Sphinkie/VintageRadio/3D models/model-view-2026-06-01.png

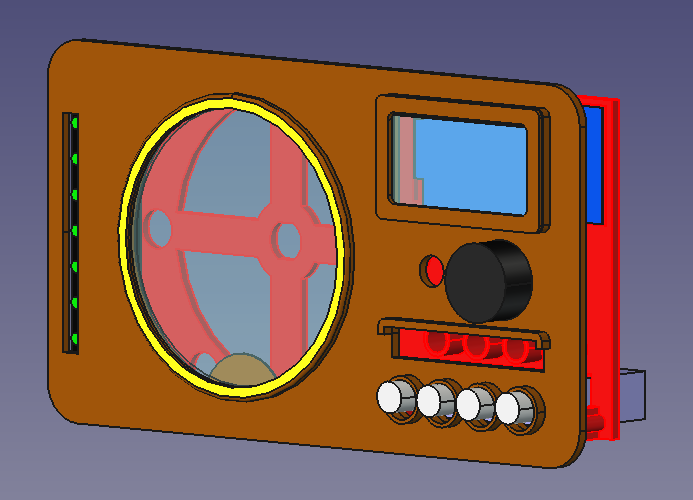
3D models/model-view-2026-06-01.png
