Sphinkie/VintageRadio/electronics/Components/datasheets/ePaper-Driver-HAT-features.png

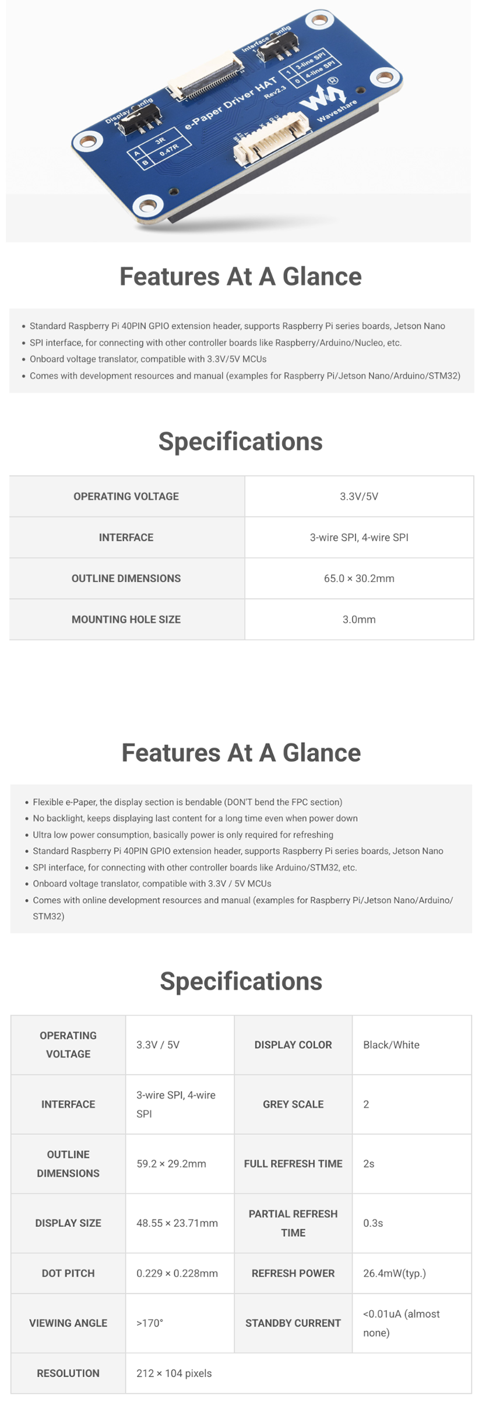
electronics/Components/datasheets/ePaper-Driver-HAT-features.png
