Sphinkie/VintageRadio/electronics/Components/datasheets/ePaper-Driver-HAT-size.png

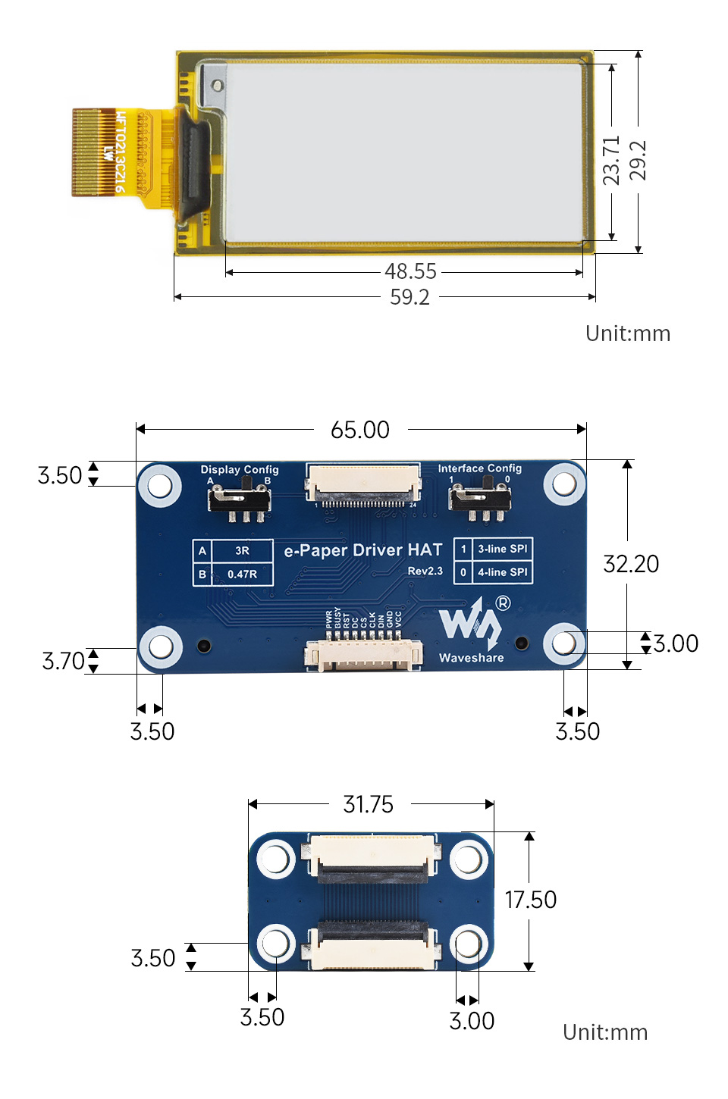
electronics/Components/datasheets/ePaper-Driver-HAT-size.png
