Sphinkie/VintageRadio/electronics/Components/datasheets/ePaper-Driver-HAT.png

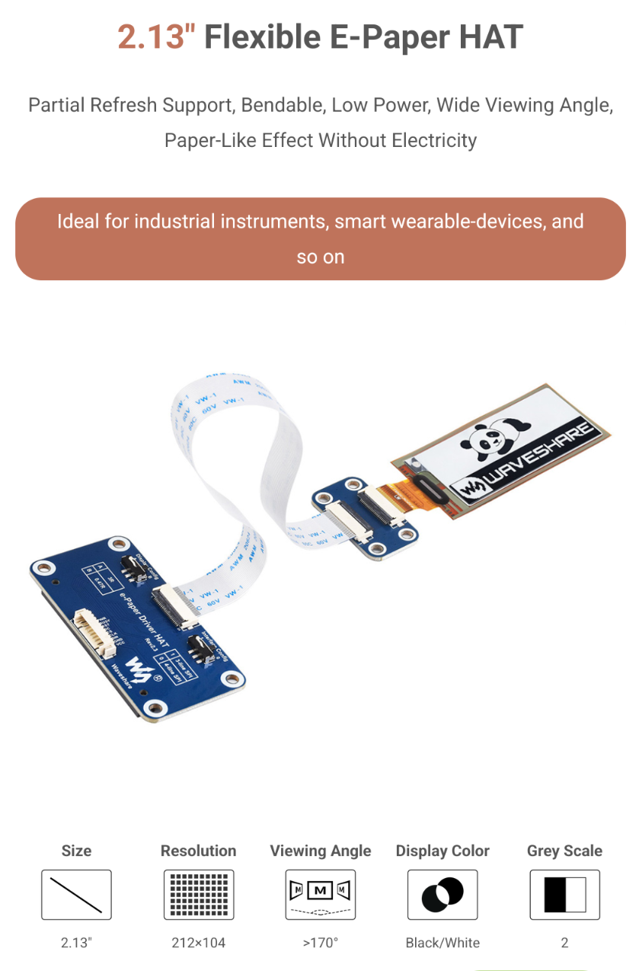
electronics/Components/datasheets/ePaper-Driver-HAT.png
