Sphinkie/VintageRadio/electronics/Components/datasheets/ePaper-Features.png

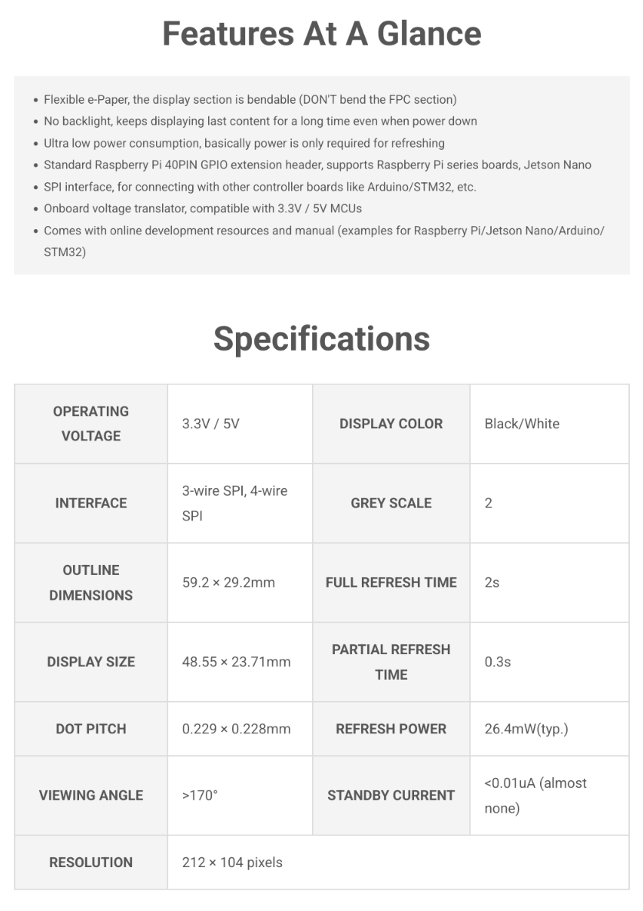
electronics/Components/datasheets/ePaper-Features.png
