Sphinkie/VintageRadio/electronics/Components/datasheets/RPI-3B-GPIO-Pinout.png

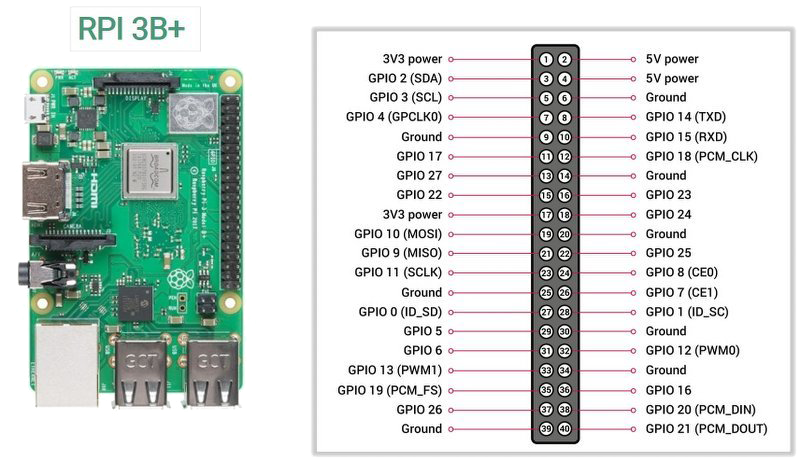
electronics/Components/datasheets/RPI-3B-GPIO-Pinout.png
