Sphinkie/VintageRadio/electronics/Components/datasheets/SN74HCS595_Pinout.png

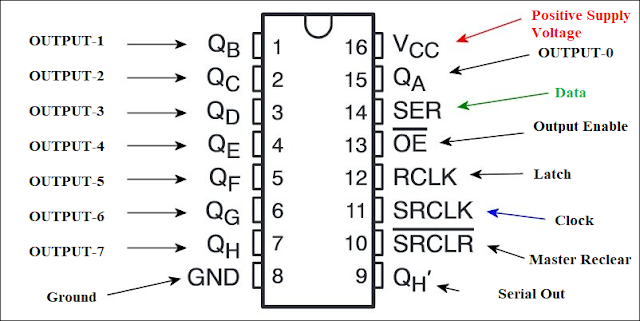
electronics/Components/datasheets/SN74HCS595_Pinout.png
