Sphinkie/VintageRadio/electronics/Components/images/ePaper-Driver-HAT-details.png

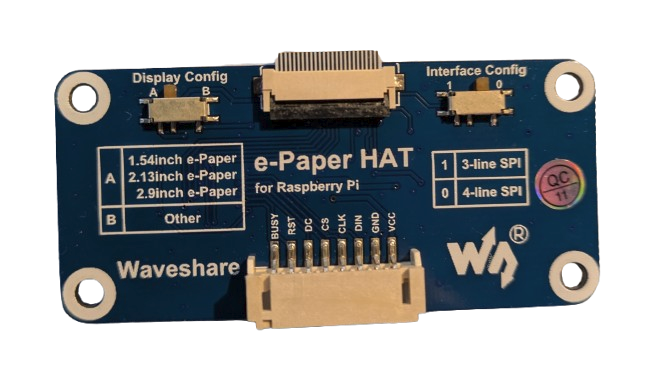
electronics/Components/images/ePaper-Driver-HAT-details.png
