Sphinkie/VintageRadio/electronics/Components/images/ePaper-Driver-HAT-wired.png

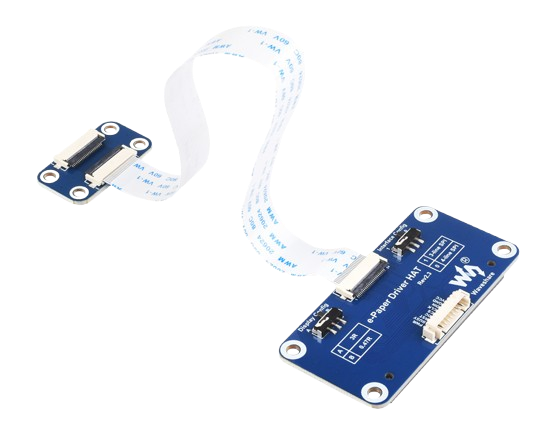
electronics/Components/images/ePaper-Driver-HAT-wired.png
