Sphinkie/VintageRadio/electronics/Components/images/ePaper-Flexible.png

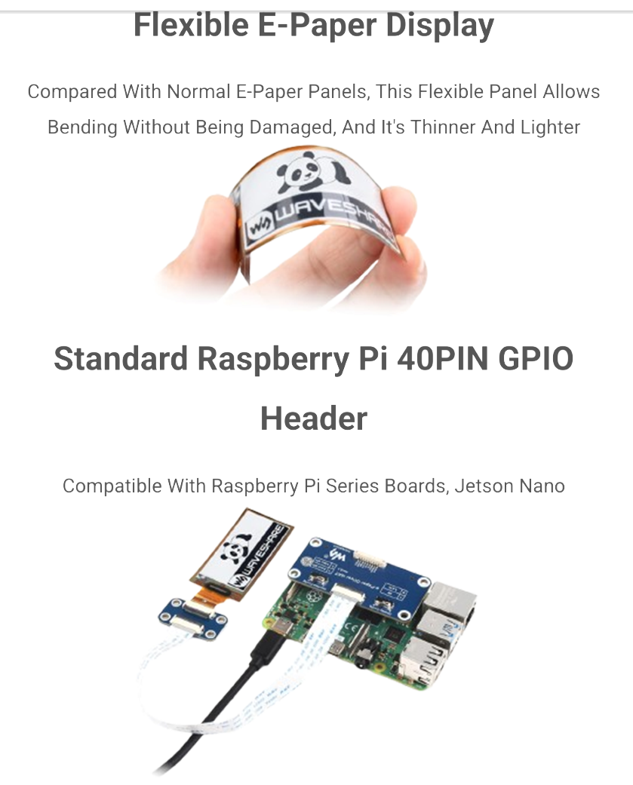
electronics/Components/images/ePaper-Flexible.png
