Sphinkie/VintageRadio/electronics/Extension boards/Extension_board.drawio.png

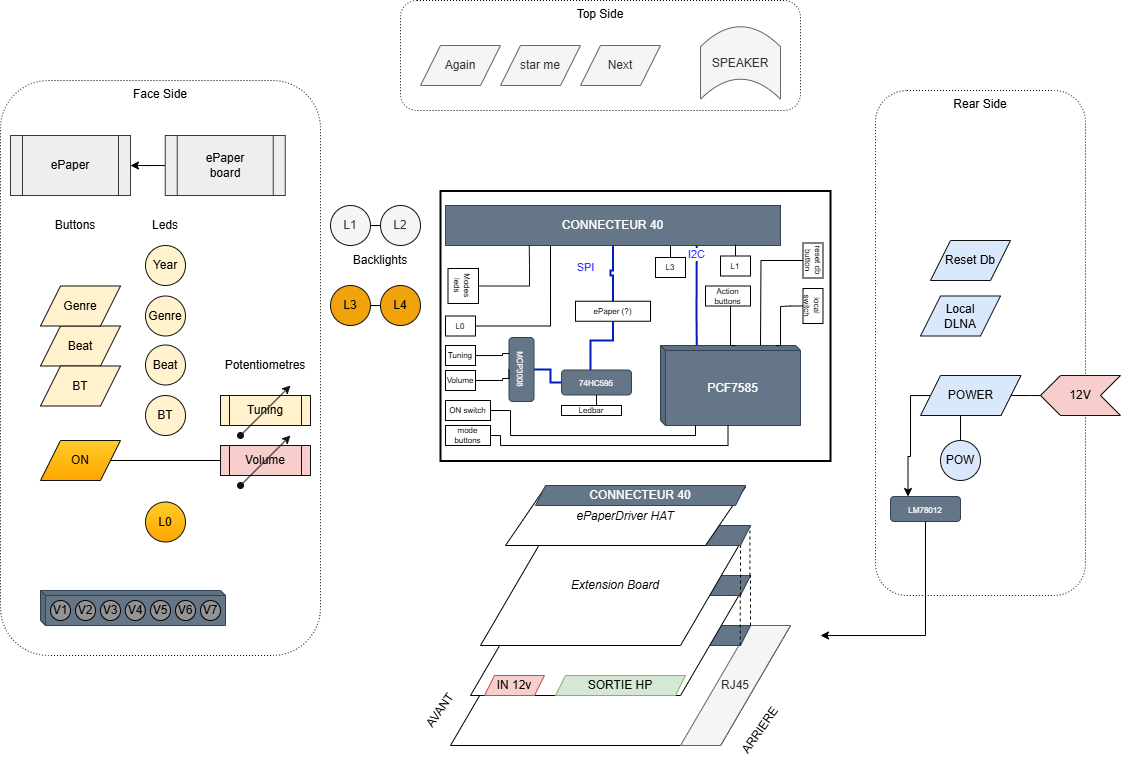
electronics/Extension boards/Extension_board.drawio.png
