Sphinkie/VintageRadio/mechanical/3mf/VintageRadio-Face_Avant.png

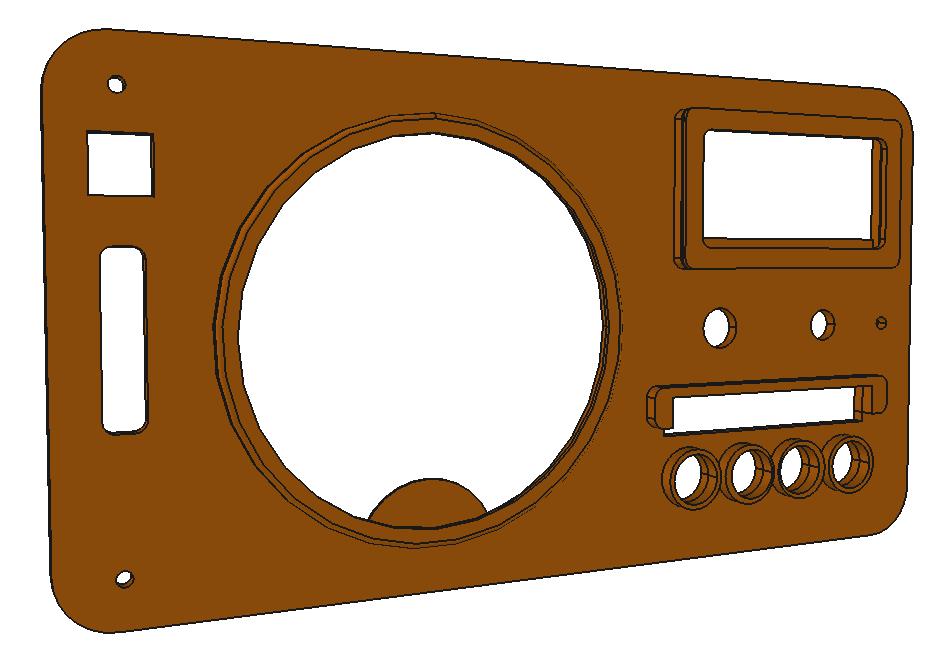
mechanical/3mf/VintageRadio-Face_Avant.png
