Sphinkie/VintageRadio/mechanical/3mf/VintageRadio-Plexi.png

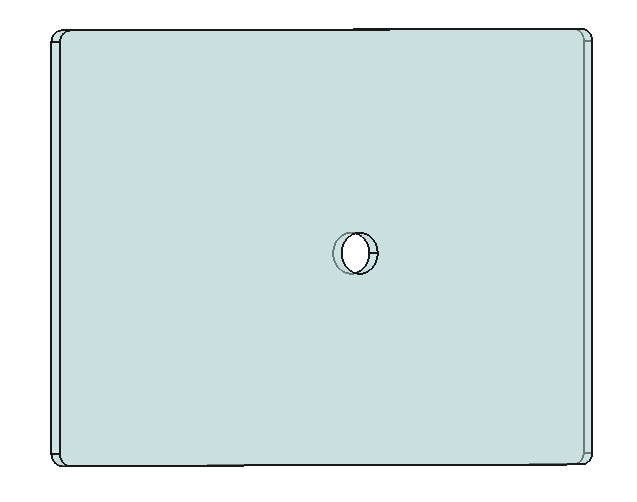
mechanical/3mf/VintageRadio-Plexi.png
