Sphinkie/VintageRadio/mechanical/3mf/VintageRadio-Support_ePaper-1.png

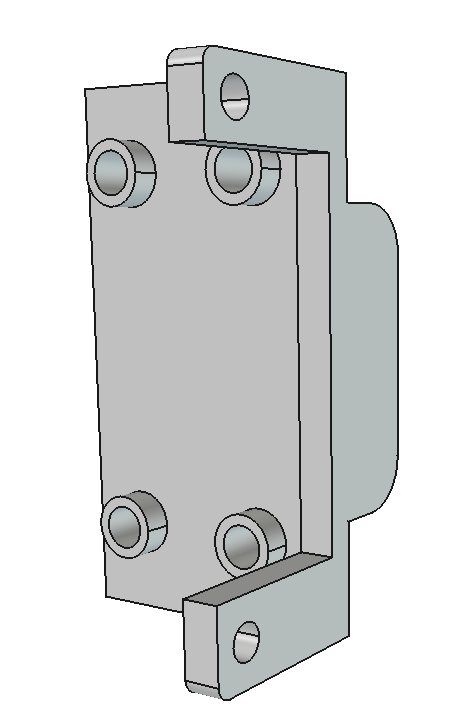
mechanical/3mf/VintageRadio-Support_ePaper-1.png
