Sphinkie/VintageRadio/mechanical/3mf/VintageRadio-Support_ePaper-3.png

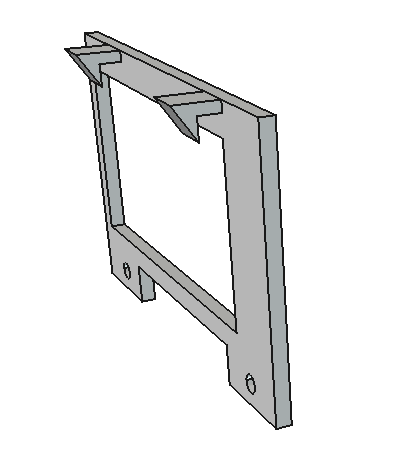
mechanical/3mf/VintageRadio-Support_ePaper-3.png
