Sphinkie/VintageRadio/mechanical/3mf/VintageRadio-Support_Leds_E10.png

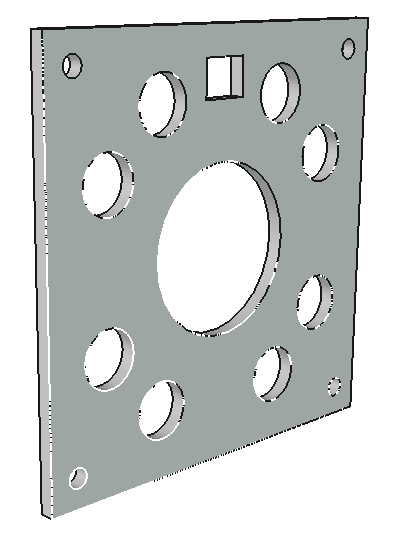
mechanical/3mf/VintageRadio-Support_Leds_E10.png
