Sphinkie/VintageRadio/mechanical/model-view-2026-04-13.png

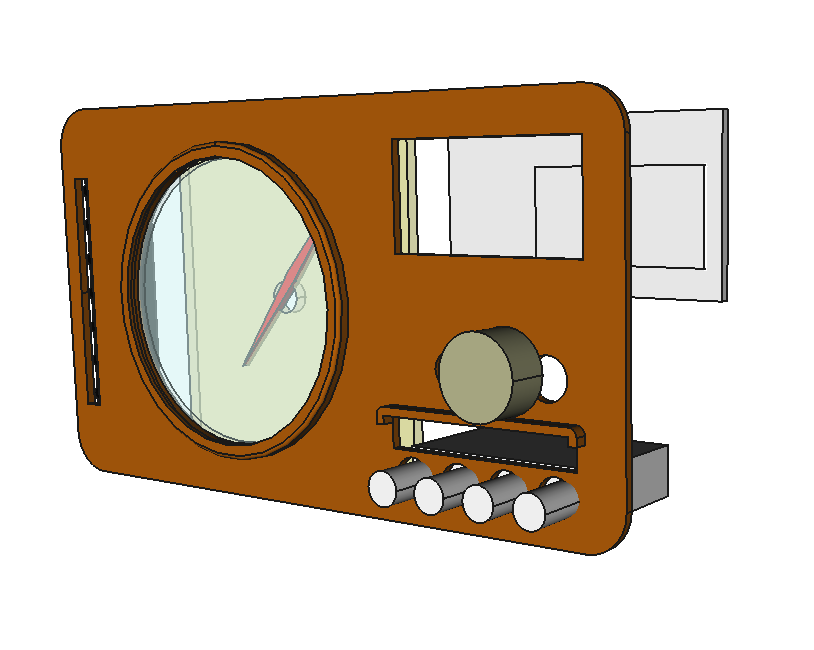
mechanical/model-view-2026-04-13.png
