Sphinkie/VintageRadio/mechanical/model-view-2026-05-31.png

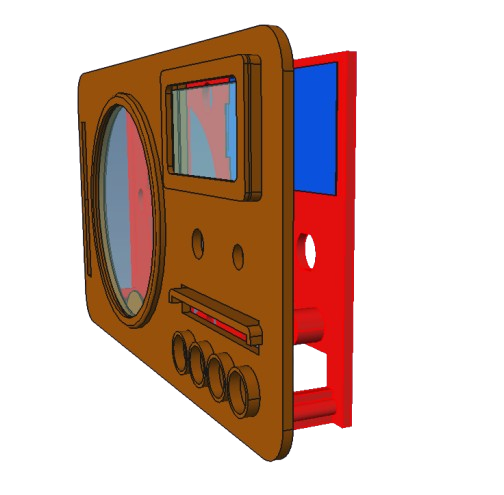
mechanical/model-view-2026-05-31.png
