Sphinkie/VintageRadio/medias/maquette.png

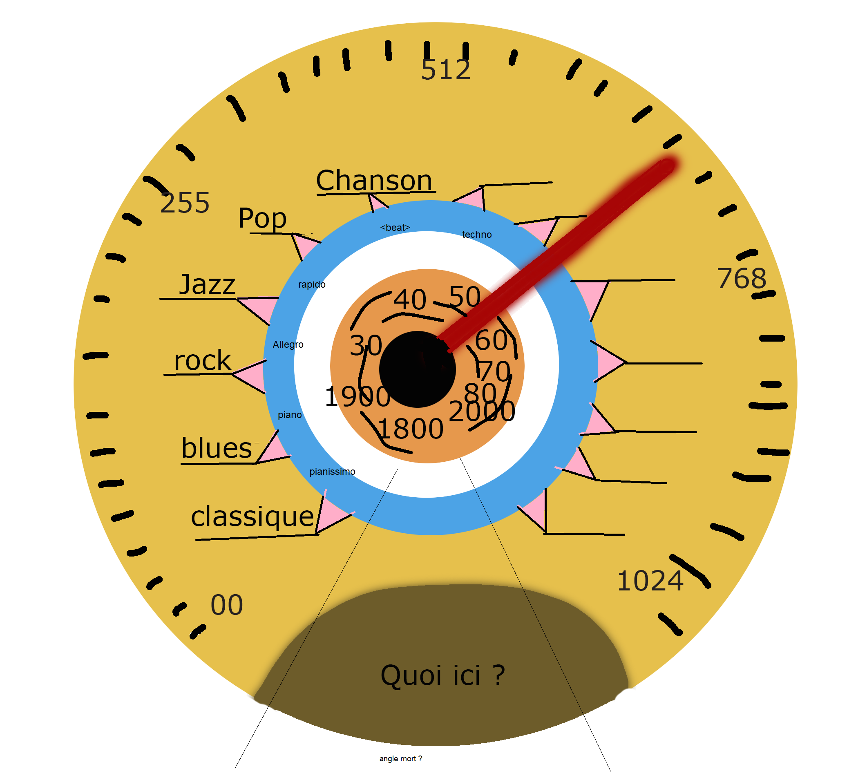
medias/maquette.png
