Sphinkie/VintageRadio/medias/pour inspiration/zoom-03.png

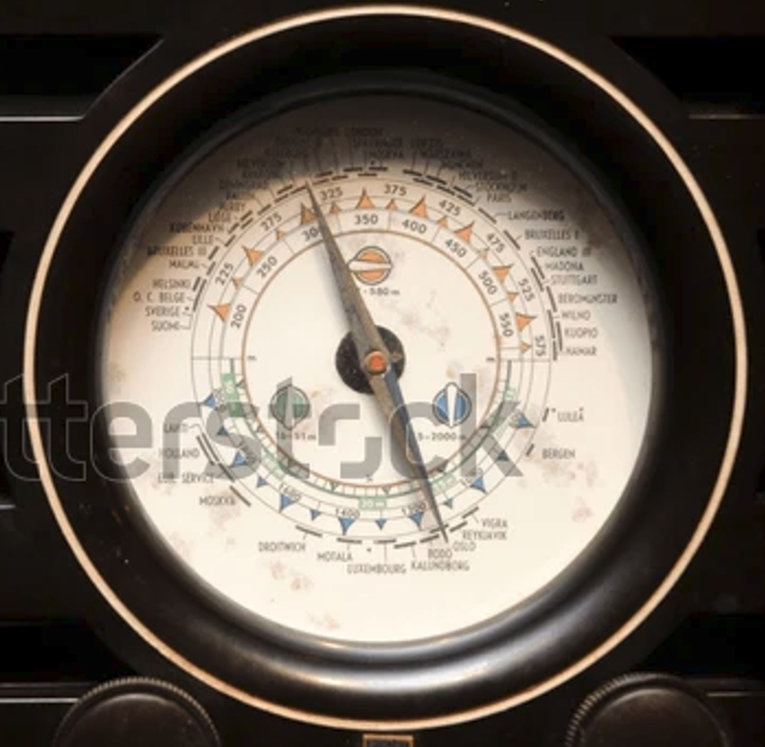
medias/pour inspiration/zoom-03.png
