Sphinkie/VintageRadio/medias/pour inspiration/zoom-04.png

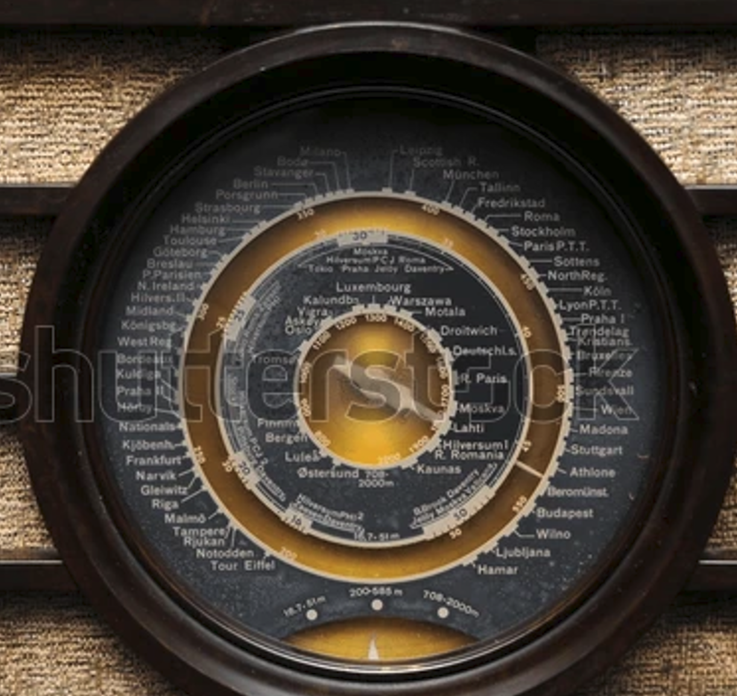
medias/pour inspiration/zoom-04.png
