Sphinkie/VintageRadio/medias/pour inspiration/zoom-09.png

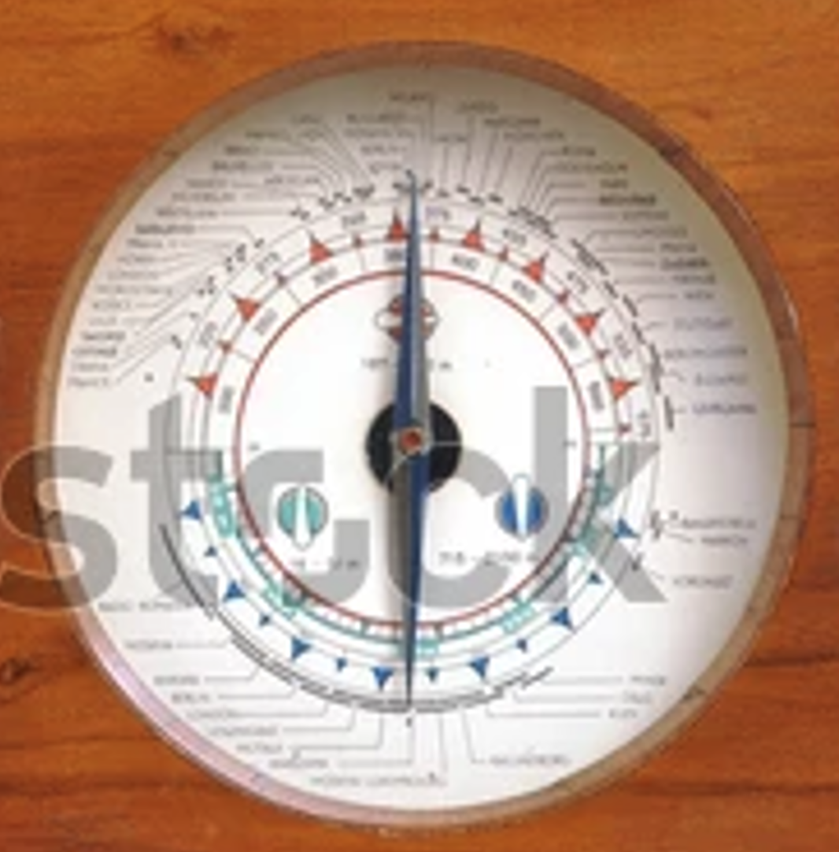
medias/pour inspiration/zoom-09.png
