Sphinkie/VintageRadio/electronics/Components/datasheets/Power-Switch.png

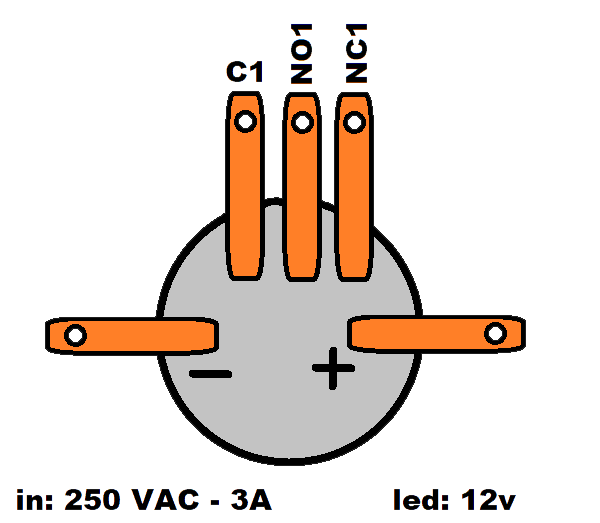
electronics/Components/datasheets/Power-Switch.png
