Sphinkie/VintageRadio/electronics/Components/datasheets/InnoMaker_TAS5713_map.jpg

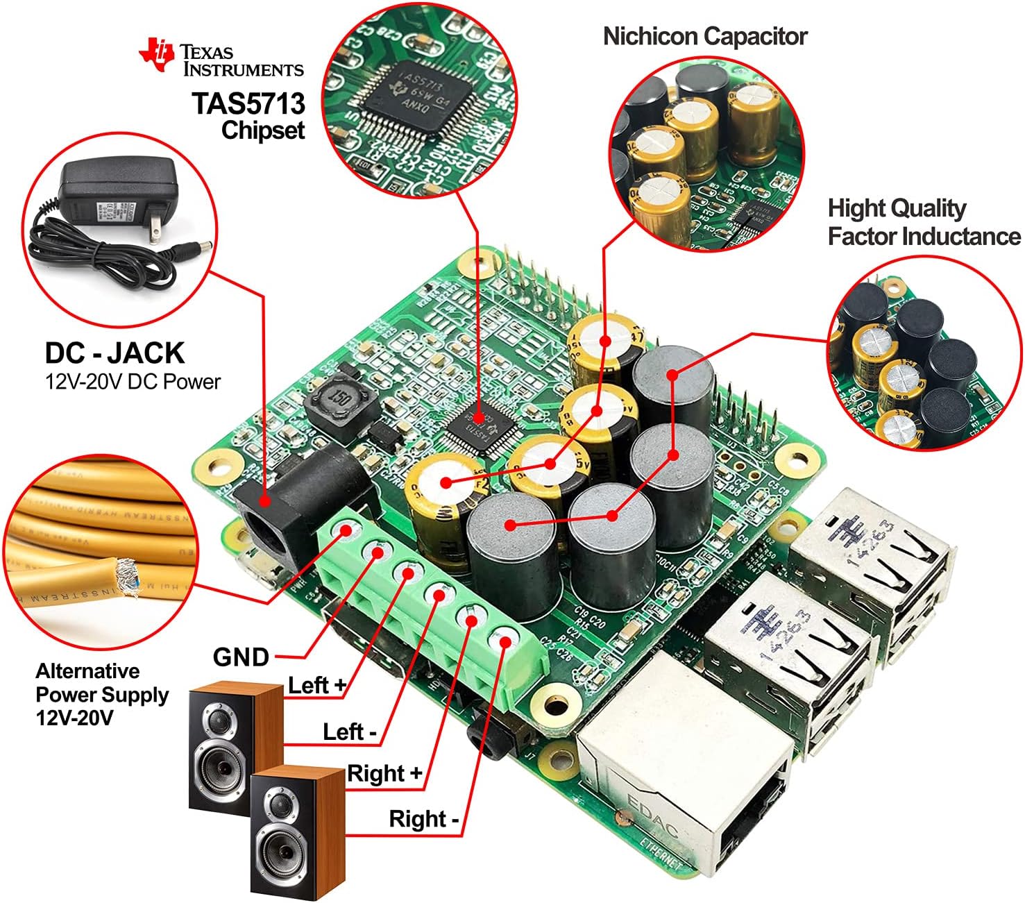
electronics/Components/datasheets/InnoMaker_TAS5713_map.jpg
