Sphinkie/VintageRadio/electronics/Components/datasheets/InnoMaker_TAS5713_pinout.jpg

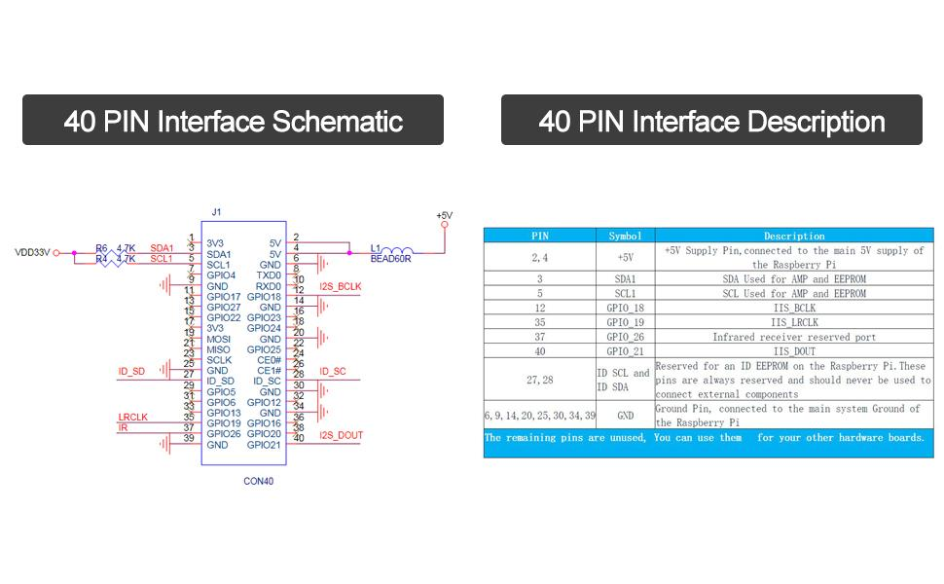
electronics/Components/datasheets/InnoMaker_TAS5713_pinout.jpg
